MOSH-Insa-Toulouse/2023-2024-4GP-TAILHAN-FERNANDES/Application Android/Connexion_bluetooth_app.png

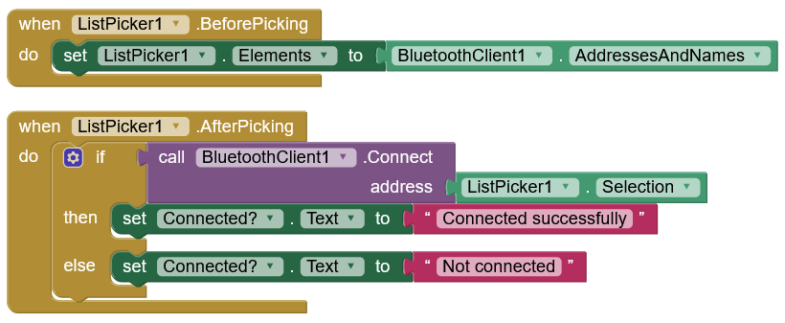
Application Android/Connexion_bluetooth_app.png
