MOSH-Insa-Toulouse/2023-2024-4GP-TAILHAN-FERNANDES/Application Android/Gestion_moteur_valeurR2_app.png

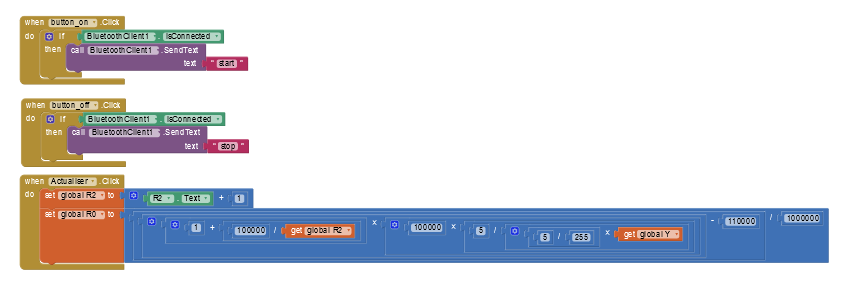
Application Android/Gestion_moteur_valeurR2_app.png
