MOSH-Insa-Toulouse/2023-2024-4GP-TAILHAN-FERNANDES/Application Android/Image application.jpeg

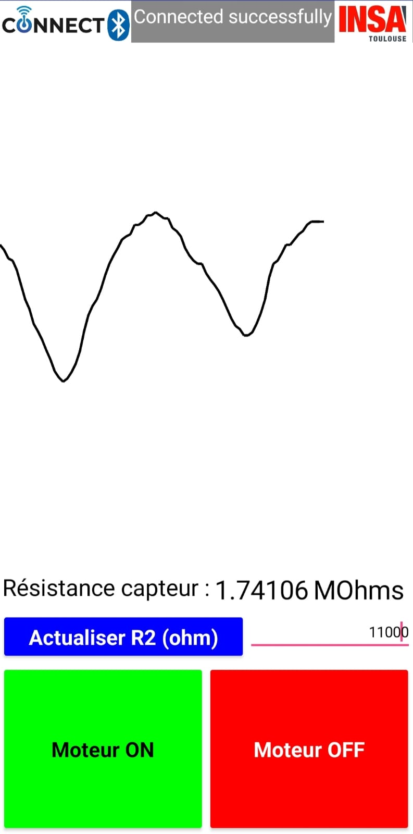
Application Android/Image application.jpeg
