MOSH-Insa-Toulouse/2023-2024-4GP-TAILHAN-FERNANDES/Application Android/Image_bluetooth_connect.png

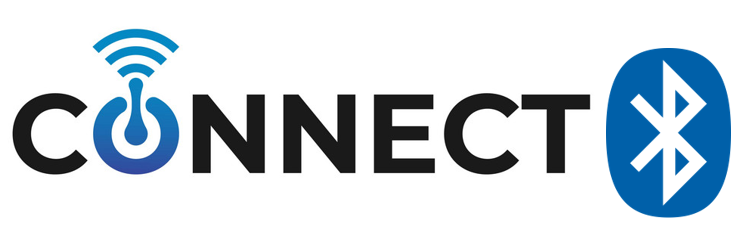
Application Android/Image_bluetooth_connect.png
