MOSH-Insa-Toulouse/2023-2024-4GP-TAILHAN-FERNANDES/Application Android/Initialisation_variables_app.png

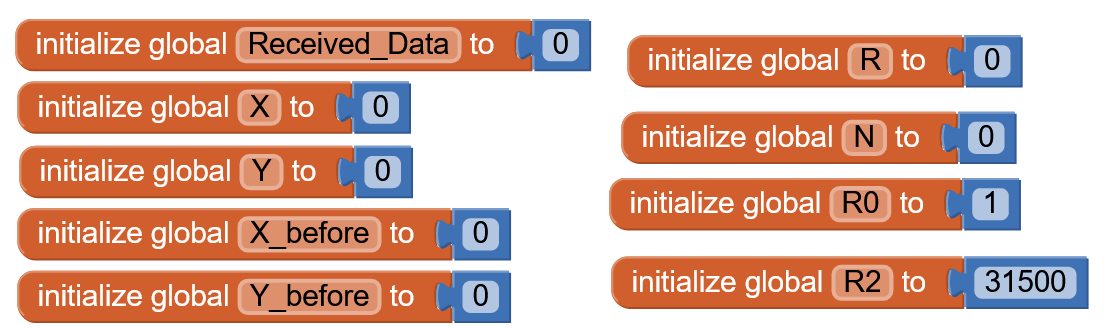
Application Android/Initialisation_variables_app.png
