MOSH-Insa-Toulouse/2023-2024-4GP-TAILHAN-FERNANDES/Arduino/Bluetooth/Branchements_module_Bluetooth.PNG

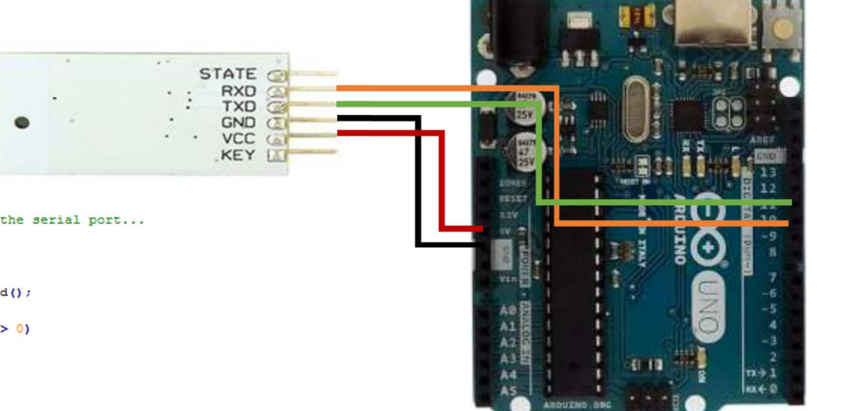
Arduino/Bluetooth/Branchements_module_Bluetooth.PNG
