MOSH-Insa-Toulouse/2023-2024-4GP-TAILHAN-FERNANDES/Arduino/Encodeur rotatoire/Branchements_encodeur_rotatoire.PNG

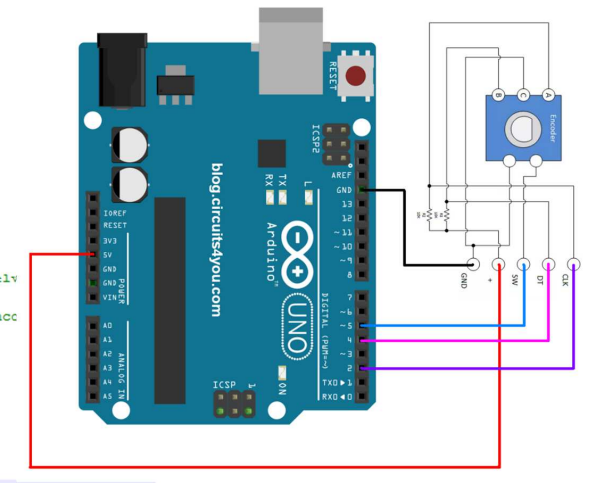
Arduino/Encodeur rotatoire/Branchements_encodeur_rotatoire.PNG
