MOSH-Insa-Toulouse/2023-2024-4GP-TAILHAN-FERNANDES/Arduino/OLED/Branchements.PNG

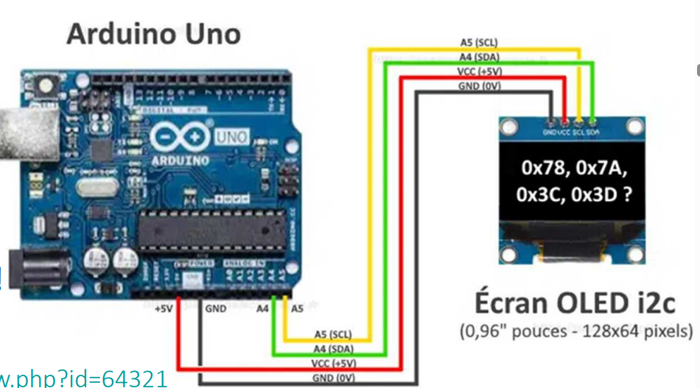
Arduino/OLED/Branchements.PNG
