MOSH-Insa-Toulouse/2023-2024-4GP-TAILHAN-FERNANDES/Arduino/Potentiomètre digital/potentiometre.PNG

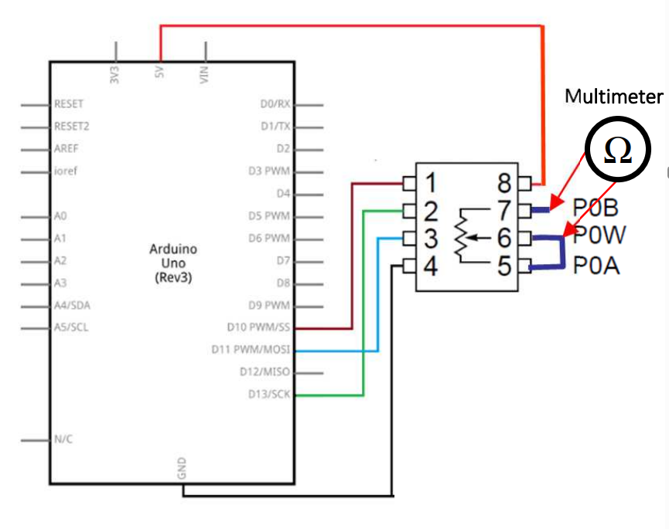
Arduino/Potentiomètre digital/potentiometre.PNG
