MOSH-Insa-Toulouse/2023-2024-4GP-TAILHAN-FERNANDES/Arduino/Potentiomètre digital/Schéma_potentiomètre.PNG

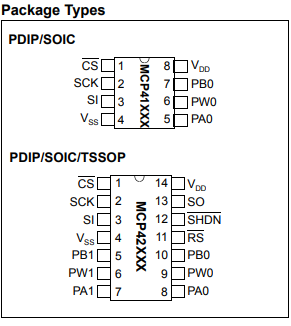
Arduino/Potentiomètre digital/Schéma_potentiomètre.PNG
