MOSH-Insa-Toulouse/2023-2024-4GP-TAILHAN-FERNANDES/Arduino/Servo_moteur/Branchement_servo_moteur.PNG

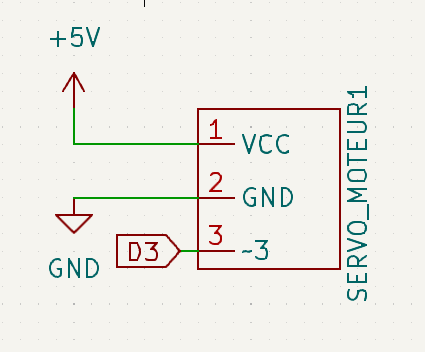
Arduino/Servo_moteur/Branchement_servo_moteur.PNG
