MOSH-Insa-Toulouse/2023-2024-4GP-TAILHAN-FERNANDES/kiCAD/modele/images_pcb/Image_electronique_analogique_LTSpice.png

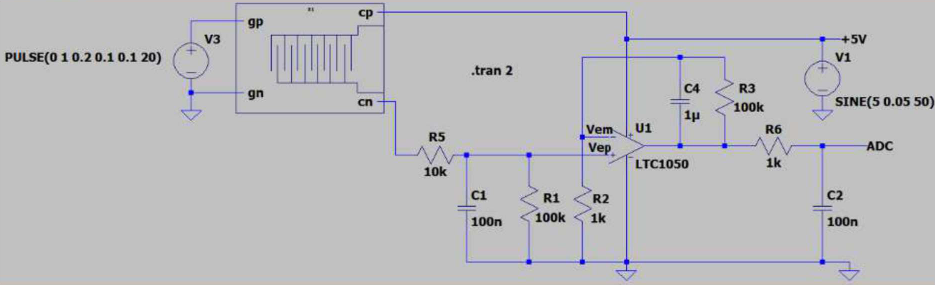
kiCAD/modele/images_pcb/Image_electronique_analogique_LTSpice.png
