MOSH-Insa-Toulouse/2023-2024-4GP-TAILHAN-FERNANDES/kiCAD/modele/images_pcb/Image_visualisation_3D_KiCad.png

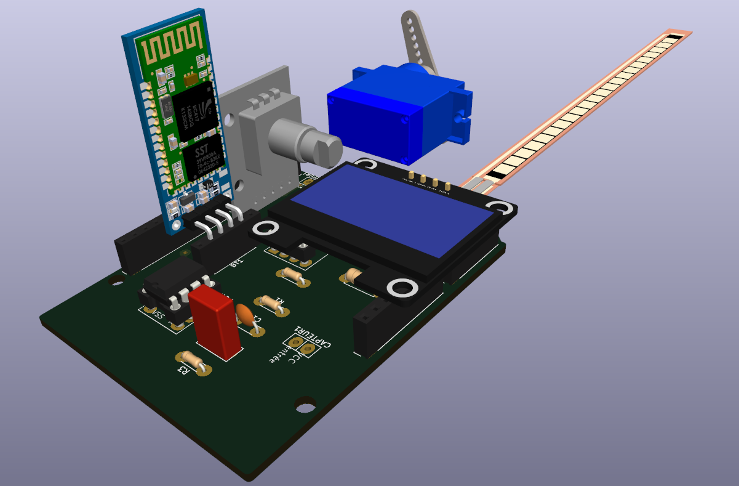
kiCAD/modele/images_pcb/Image_visualisation_3D_KiCad.png
