MOSH-Insa-Toulouse/2023-2024-4GP-TAILHAN-FERNANDES/kiCAD/modele/servo-motor-110.snapshot.1/Servo Motor-1.JPG

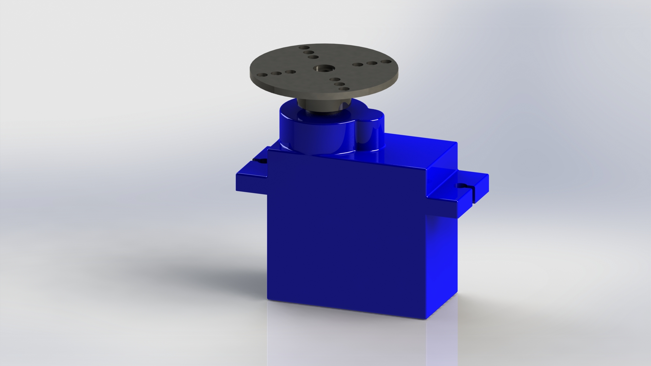
kiCAD/modele/servo-motor-110.snapshot.1/Servo Motor-1.JPG
