MOSH-Insa-Toulouse/2023-2024-4GP-TAILHAN-FERNANDES/kiCAD/modele/servo-motor-110.snapshot.1/Gear-4.STEP

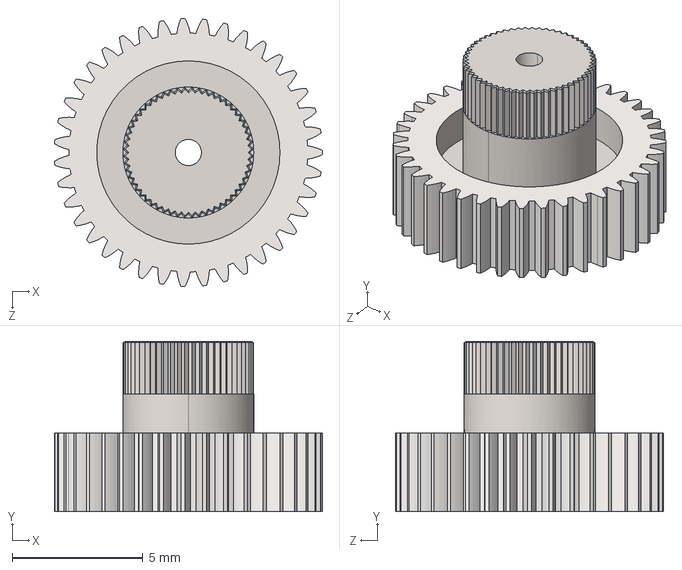
[picture p35: CAD file, 2024-05-17]
kiCAD/modele/servo-motor-110.snapshot.1/Gear-4.STEP
10.2 x 6.50 x 10.2 mm
