MOSH-Insa-Toulouse/2023-2024-4GP-TAILHAN-FERNANDES/kiCAD/modele/servo-motor-110.snapshot.1/Part_7.STEP

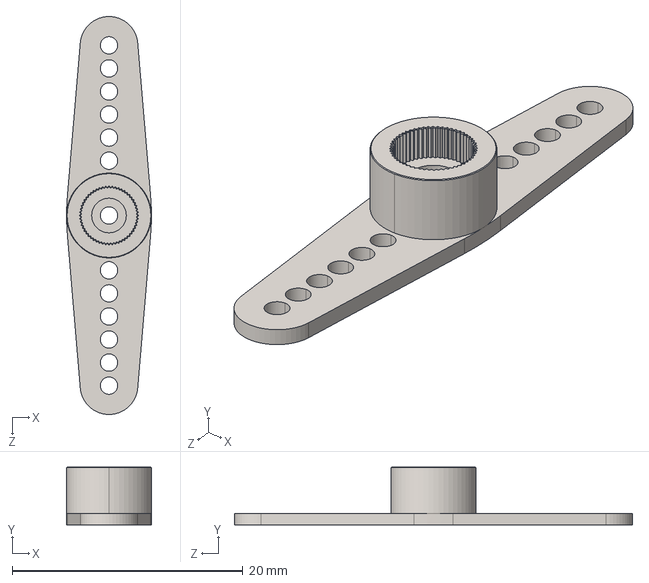
[picture p36: CAD file, 2024-05-17]
kiCAD/modele/servo-motor-110.snapshot.1/Part_7.STEP
7.36 x 5.00 x 34.5 mm
