MOSH-Insa-Toulouse/2023-2024-4GP-TAILHAN-FERNANDES/kiCAD/modele/servo-motor-110.snapshot.1/Part_6-Brushing 1.STEP

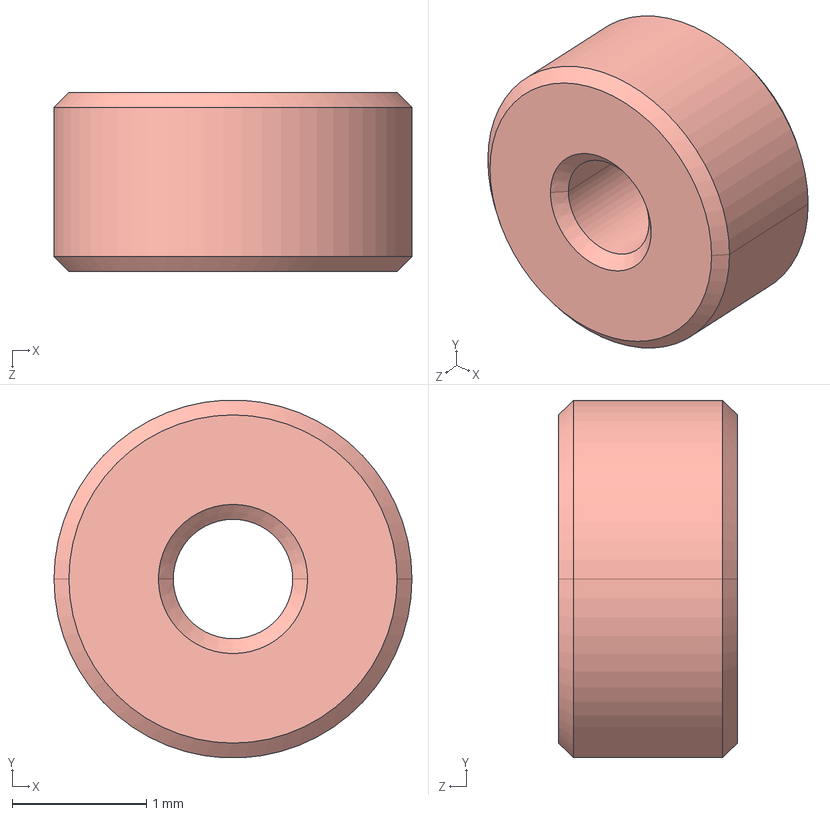
[picture p37: CAD file, 2024-05-17]
kiCAD/modele/servo-motor-110.snapshot.1/Part_6-Brushing 1.STEP
2.67 x 2.67 x 1.33 mm
