MOSH-Insa-Toulouse/2023-2024-4GP-TAILHAN-FERNANDES/kiCAD/modele/servo-motor-110.snapshot.1/Part_4-Magnet.STEP

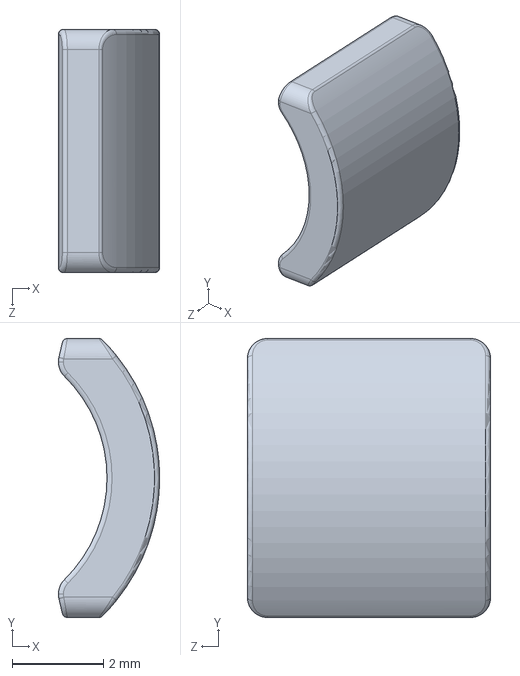
[picture p38: CAD file, 2024-05-17]
kiCAD/modele/servo-motor-110.snapshot.1/Part_4-Magnet.STEP
2.22 x 6.12 x 5.34 mm
