MOSH-Insa-Toulouse/2023-2024-4GP-TAILHAN-FERNANDES/kiCAD/modele/servo-motor-110.snapshot.1/DC_Motor-Casing.STEP

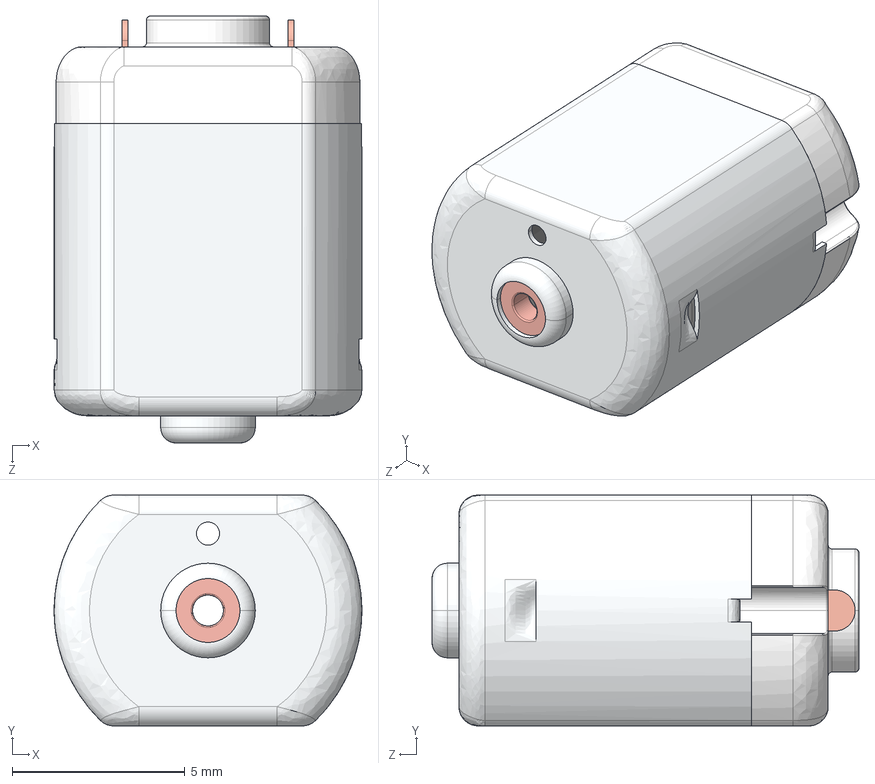
[picture p39: CAD file, 2024-05-17]
kiCAD/modele/servo-motor-110.snapshot.1/DC_Motor-Casing.STEP
8.90 x 6.68 x 12.3 mm
Part_2-Cover
Part_6-Brushing 1
Part_3-End Cover x 2
Part_1-Housing
Part_4-Magnet x 2
Part_5-Spacer
Part_7-Brushing 2 Shaft Fixture
