MOSH-Insa-Toulouse/2023-2024-4GP-TAILHAN-FERNANDES/kiCAD/modele/servo-motor-110.snapshot.1/Part_3-End Cover.STEP

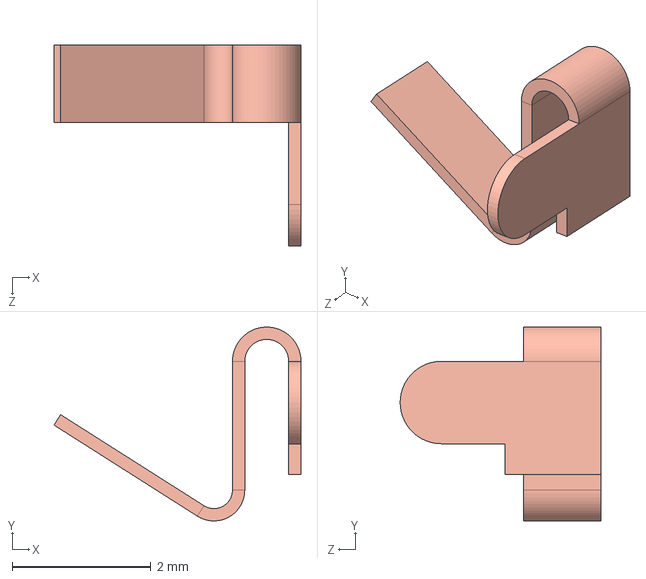
[picture p40: CAD file, 2024-05-17]
kiCAD/modele/servo-motor-110.snapshot.1/Part_3-End Cover.STEP
3.56 x 2.79 x 2.89 mm
