MOSH-Insa-Toulouse/2023-2024-4GP-TAILHAN-FERNANDES/kiCAD/modele/servo-motor-110.snapshot.1/Part_2-Cover.STEP

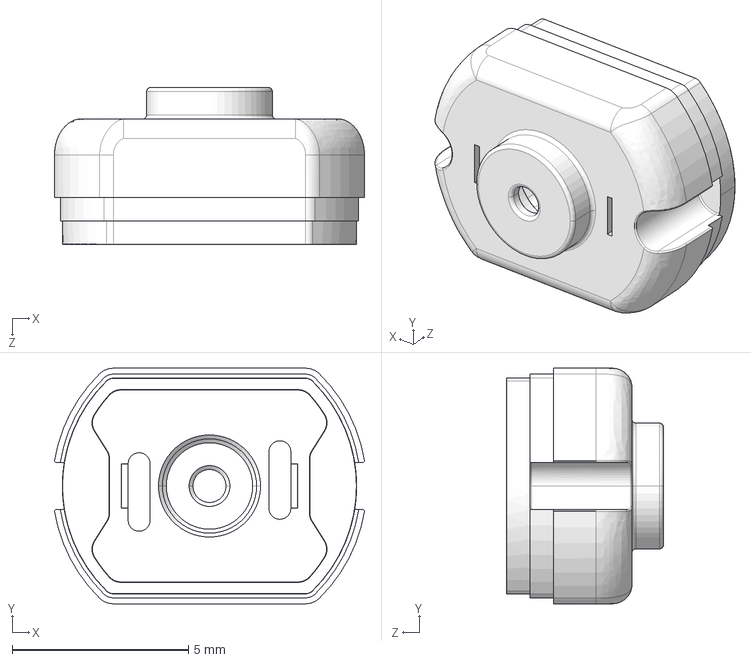
[picture p41: CAD file, 2024-05-17]
kiCAD/modele/servo-motor-110.snapshot.1/Part_2-Cover.STEP
8.78 x 6.68 x 4.45 mm
