MOSH-Insa-Toulouse/2023-2024-4GP-TAILHAN-FERNANDES/Arduino/Capteur/capteur/capteur.ino

/*
  AnalogReadSerial

  Reads an analog input on pin 0, prints the result to the Serial Monitor.
  Graphical representation is available using Serial Plotter (Tools > Serial Plotter menu).
  Attach the center pin of a potentiometer to pin A0, and the outside pins to +5V and ground.

  This example code is in the public domain.

  https://www.arduino.cc/en/Tutorial/BuiltInExamples/AnalogReadSerial
*/

// the setup routine runs once when you press reset:
void setup() {
  // initialize serial communication at 9600 bits per second:
  Serial.begin(9600);
}

// the loop routine runs over and over again forever:
void loop() {
  // read the input on analog pin 0:
  int sensorValue = analogRead(A0);
  // print out the value you read:
  Serial.println(sensorValue);
  delay(40);  // delay in between reads for stability
}
/*
  Fichier :       afficherTexteSsd1306.ino
  Description :   Affiche du texte de test, sur un écran OLED i2c de 128x64 pixels,
                  fonctionnant avec un contrôleur SSD1306
  Auteur :        Jérôme TOMSKI (https://passionelectronique.fr/)
  Créé le :       26.07.2021
*/
